AronLapp/Grab-IT-on-Steroids/CAD/Motor5/encoder_mount/encoder_mount.FCStd

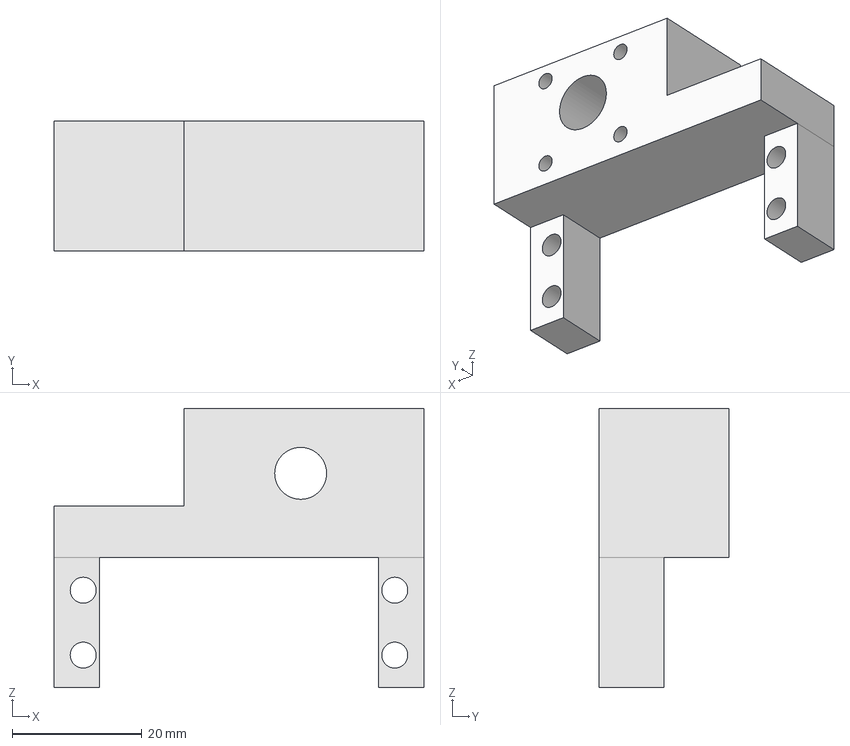
[picture p20: CAD file, 2025-08-22]
CAD/Motor5/encoder_mount/encoder_mount.FCStd
57.0 x 20.0 x 43.0 mm
