AronLapp/Grab-IT-on-Steroids/CAD/Motor6/encoder_holder/encoder_holder.FCStd

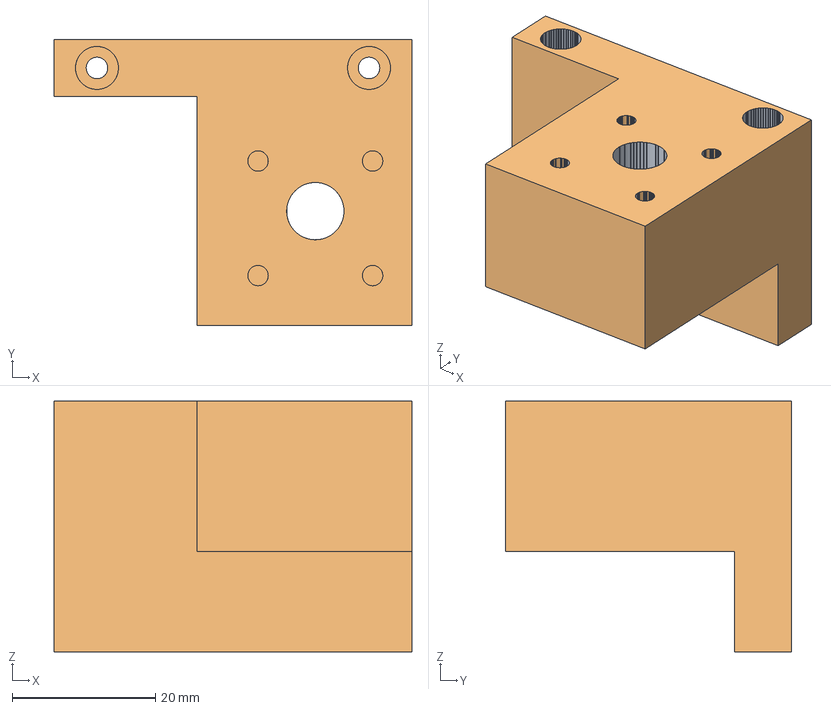
[picture p21: CAD file, 2025-08-22]
CAD/Motor6/encoder_holder/encoder_holder.FCStd
50.0 x 40.0 x 35.0 mm
Body (Meshed)
