AronLapp/Grab-IT-on-Steroids/CAD/Motor6/magnet_holder/magnet_holder.FCStd

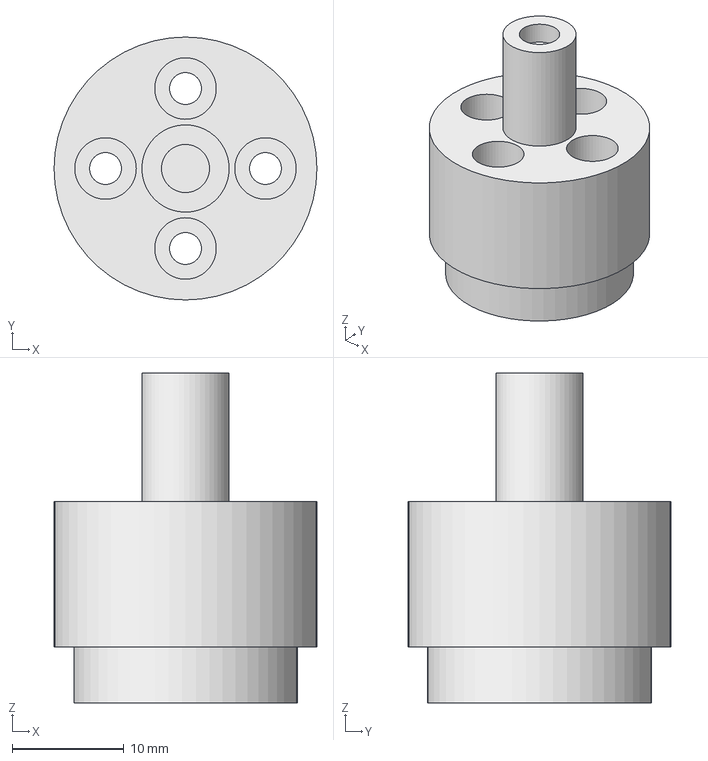
[picture p22: CAD file, 2025-08-22]
CAD/Motor6/magnet_holder/magnet_holder.FCStd
23.5 x 23.5 x 29.5 mm
