AronLapp/Grab-IT-on-Steroids/CAD/circuitboard_enclosure/v2.FCStd

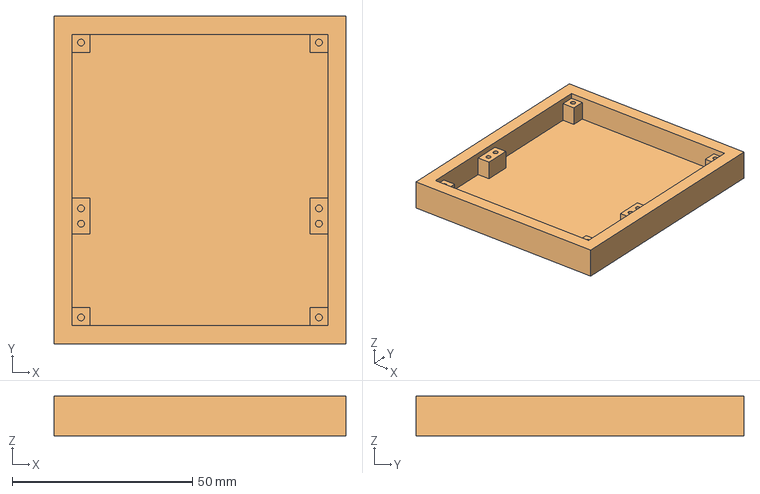
[picture p23: CAD file, 2025-08-22]
CAD/circuitboard_enclosure/v2.FCStd
81.0 x 91.0 x 11.0 mm
Body (Meshed)
