AronLapp/Grab-IT-on-Steroids/CAD/Motor2/encoder_mount/general_mount_v4_3.stl

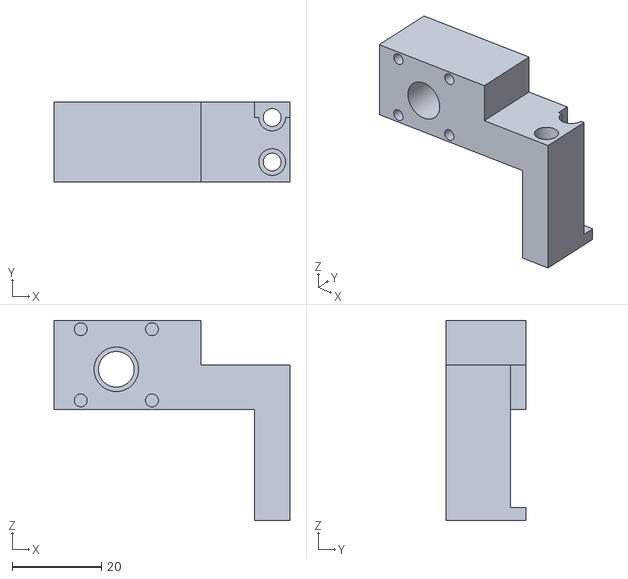
[picture p24: CAD file, 2025-08-08]
CAD/Motor2/encoder_mount/general_mount_v4_3.stl
53.0 x 18.0 x 45.0
