AronLapp/Grab-IT-on-Steroids/CAD/Motor3/basic_spacer_enc/basic_spacer_enc.stl

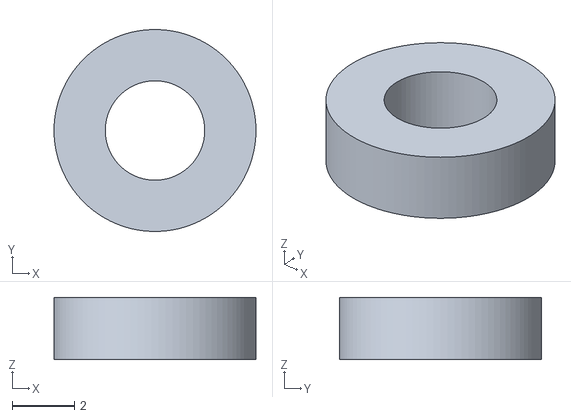
[picture p25: CAD file, 2025-08-08]
CAD/Motor3/basic_spacer_enc/basic_spacer_enc.stl
6.50 x 6.50 x 2.00
